alphaseneca/stairlight_controller/images/image1.JPG

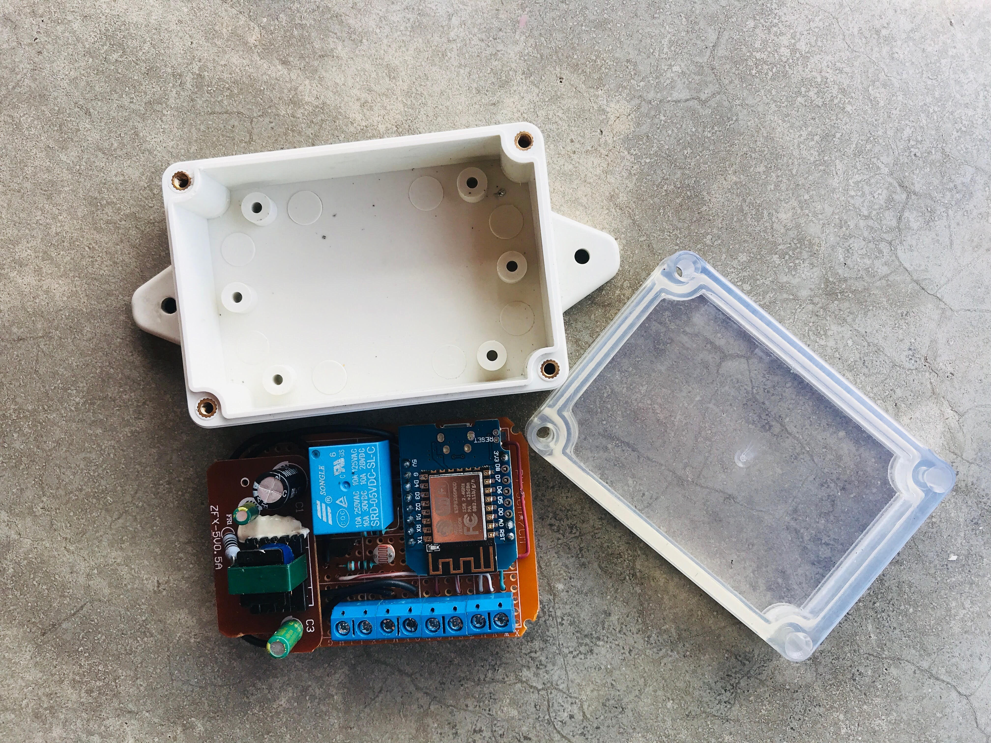
images/image1.JPG
